sbambach/MarksEnclosureHelper/docpix/surface-pvw.png

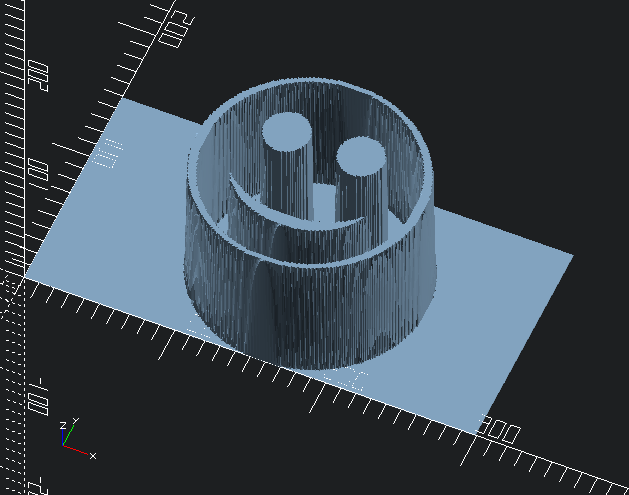
docpix/surface-pvw.png
