sbambach/MarksEnclosureHelper/example-minitin/example-minitin-catch-1.jpg

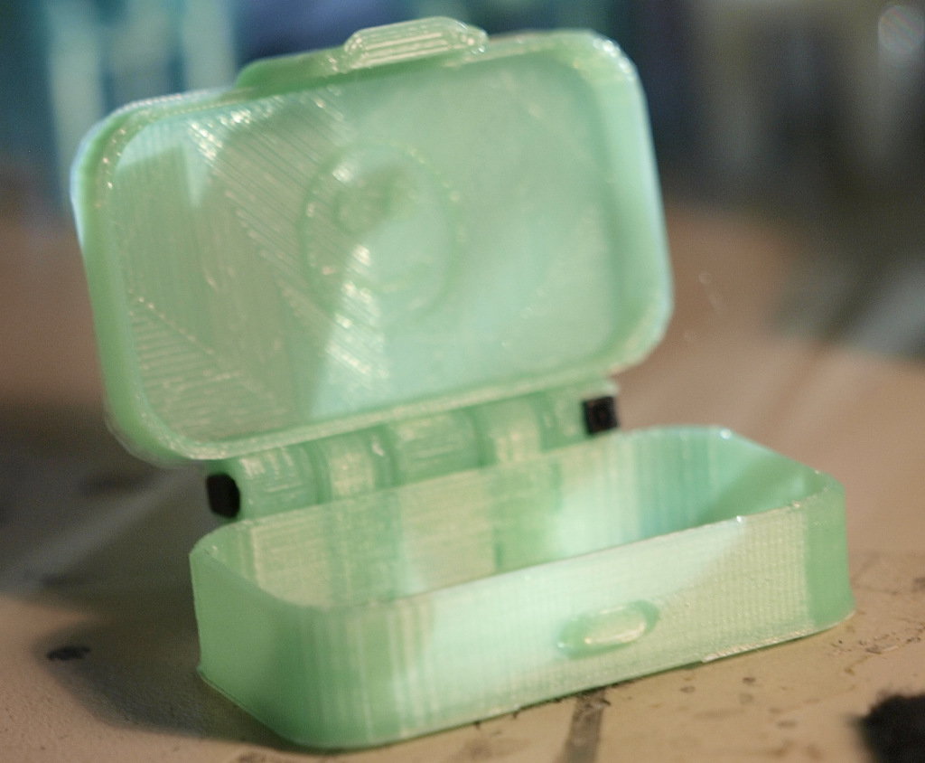
example-minitin/example-minitin-catch-1.jpg
