sbambach/MarksEnclosureHelper/example-minitin/example-minitin-catch-3.jpg

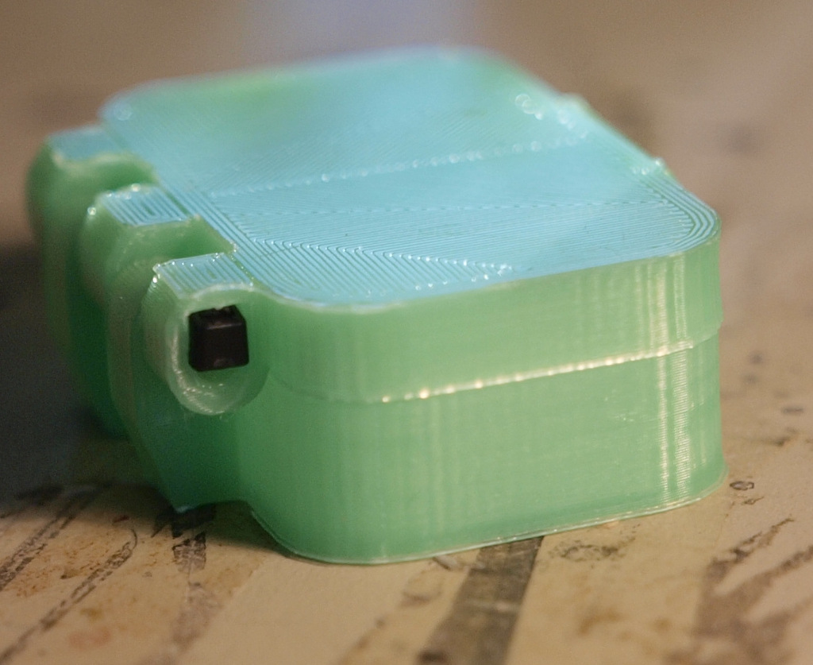
example-minitin/example-minitin-catch-3.jpg
