sbambach/MarksEnclosureHelper/example-minitin/example-minitin-magwart-2.jpg

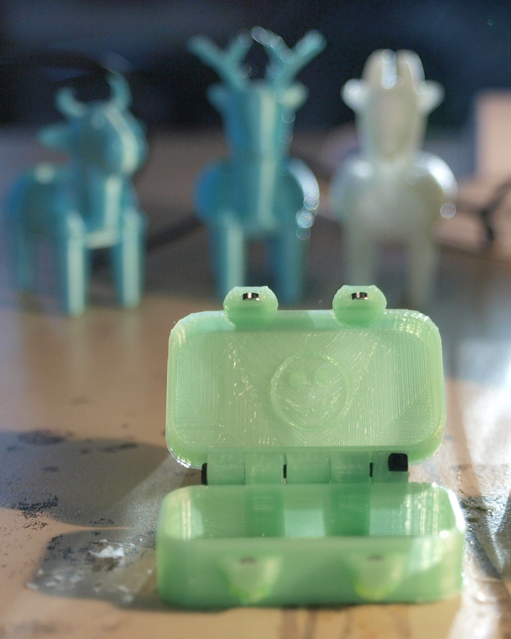
example-minitin/example-minitin-magwart-2.jpg
