sbambach/MarksEnclosureHelper/example-minitin/smile.png

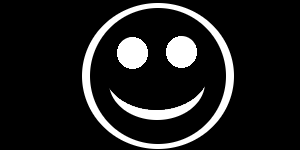
example-minitin/smile.png
