sbambach/MarksEnclosureHelper/example-needlekeeper/example-needlekeeper-front.jpg

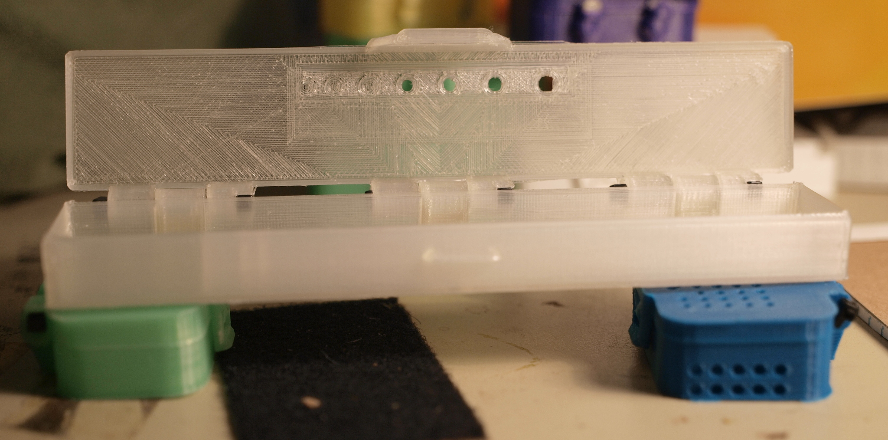
example-needlekeeper/example-needlekeeper-front.jpg
