sbambach/MarksEnclosureHelper/example-partbox/example-partbox-back.jpg

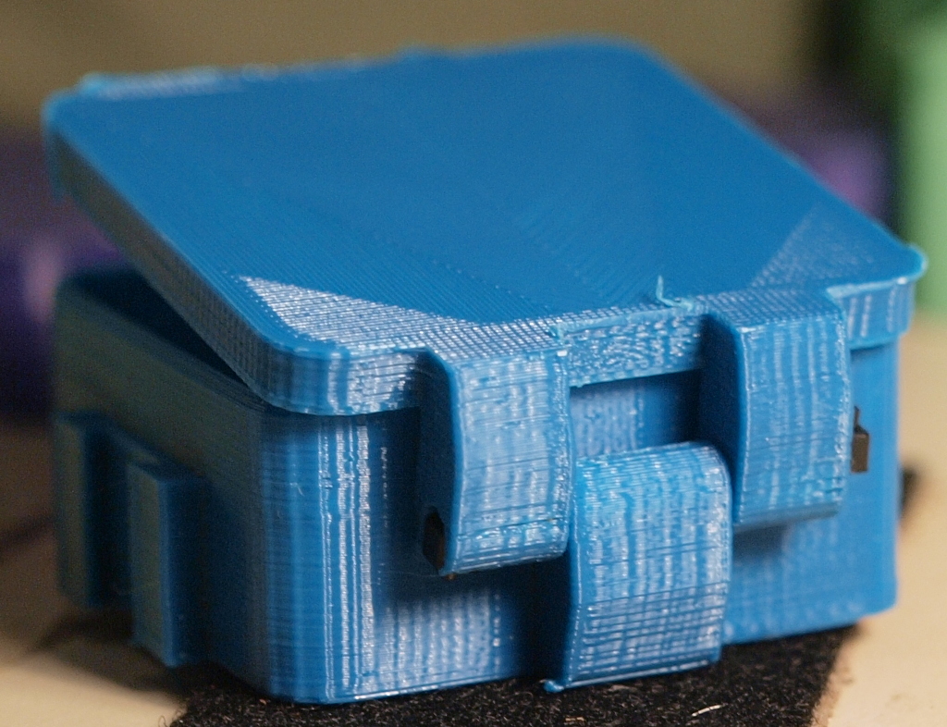
example-partbox/example-partbox-back.jpg
